andr00d/epd_watch/code/src/pages.rs

pub mod pages;
pub mod state;
mod core_pages;
mod snake;

use crate::shared_data::SharedData;
use crate::pages::state::PageState;

pub struct Pages
{
    curr_page: fn(&mut SharedData) -> (),
    curr_state: PageState,  
}
