andr00d/epd_watch/code/pc_test/src/pages.rs

#[path = "../../src/pages/pages.rs"]
pub mod pages;

#[path = "../../src/pages/state.rs"]
pub mod state;

#[path = "../../src/pages/core_pages.rs"]
mod core_pages;

#[path = "../../src/pages/snake.rs"]
mod snake;

use crate::shared_data::SharedData;
use crate::pages::state::PageState;

pub struct Pages
{
    curr_page: fn(&mut SharedData) -> (),
    curr_state: PageState,  
}
